thmjpr/nano_stepper/firmware/stepper_nano_zero/stepper_controller.h

/**********************************************************************
 *      Author: tstern
 *
 *	Misfit Tech invests time and resources providing this open source code,
 *	please support Misfit Tech and open-source hardware by purchasing
 *	products from Misfit Tech, www.misifittech.net!
 *
 *	Written by Trampas Stern  for Misfit Tech.
 *	BSD license, check license.txt for more information
 *	All text above, must be included in any redistribution
 *********************************************************************/
#ifndef __STEPPER_CONTROLLER_H__
#define __STEPPER_CONTROLLER_H__

#include "syslog.h"
#include "board.h"
#include "calibration.h"
#include "nonvolatile.h"

#ifdef AS5047D_ENCODER
	#include "as5047d.h"
#elif defined A1333_DRIVER
	#include "a1333.h"
#else
	#error 
#endif

#ifdef A5995_DRIVER
	#include "A5995.h"
#elif defined  STEPPER_10A
	#include "fet_driver.h"			//for the NEMA23 10A
#elif defined A4954_DRIVER
	#include "A4954.h"
#else
	#error "driver not defined"
#endif

#define N_DATA (1024)

enum class stepCtrlError {
	No_ERROR =		0,
	No_POWER =		1, //no power to motor
	No_CAL =		2, //calibration not set
	No_ENCODER =	3, //encoder not working
};

//
typedef struct {
		int32_t Kp;
		int32_t Ki;
		int32_t Kd;
} PID_t;

//
 typedef __attribute__((aligned(4))) struct {
	  int32_t microSecs;
	  int32_t desiredLoc;
	  int32_t actualLoc;
	  int32_t angle;
	  int32_t ma;
} Location_t;

//
typedef struct {
	  int32_t angle;
	  int32_t ma;
}Control_t;

#define MAX_NUM_LOCATIONS (64) //maximum number of locations to buffer

//this scales the PID parameters from Flash to floating point to fixed point int32_t values
#define CTRL_PID_SCALING (1024)

class LCD;		//Forward declaration

class StepperCtrl 
{
	private:
		volatile bool enableFeedback; //true if we are using PID control algorithm
		AS5047D encoder;
#ifdef NEMA_23_10A_HW
		FetDriver stepperDriver;
#elif defined A5995_DRIVER
		A5995 stepperDriver;
#elif defined A4954_DRIVER
		A4954 stepperDriver;
#endif

		uint16_t startUpEncoder;
		volatile int32_t ticks = 0;
		volatile Location_t locs[MAX_NUM_LOCATIONS];
		volatile int32_t locReadIndx = 0;
		volatile int32_t locWriteIndx = 0;

		volatile MotorParams_t motorParams;
		volatile SystemParams_t systemParams;
		volatile bool enabled;

		volatile int32_t loopTimeus; //time to run loop in microseconds

		volatile PID_t sPID; //simple control loop PID parameters
		volatile PID_t pPID; //positional current based PID control parameters
		volatile PID_t vPID; //velocity PID control parameters

		volatile int64_t numSteps; //this is the number of steps we have taken from our start angle

		volatile int32_t loopError;

		volatile int64_t currentLocation; //estimate of the current location from encoder feedback
		// the current location lower 16 bits is angle (0-360 degrees in 65536 steps) while upper
		// bits is the number of full rotations.

		//this is used for the velocity PID feedback
		// units are in Angles/sec where 1 Angle=360deg/65536
		volatile int64_t velocity;

		int64_t zeroAngleOffset = 0;

		//does linear interpolation of the encoder calibration table
		int32_t getAngleCalibration(int32_t encoderAngle);

		//updates the currentMeasuredAngle with our best guess where we are
		Angle sampleAngle(void);
		Angle sampleMeanEncoder(int32_t numSamples);

		float measureStepSize(void); //steps motor and estimates step size
		uint32_t measureMaxCalibrationError(void);
		void setLocationFromEncoder(void);

		void  motorReset(void);
		void updateStep(int dir, uint16_t steps);

		bool pidFeedback(int64_t desiredLoc, int64_t currentLoc, Control_t *ptrCtrl);
		bool simpleFeedback(int64_t desiredLoc, int64_t currentLoc,Control_t *ptrCtrl);
		bool vpidFeedback(int64_t desiredLoc, int64_t currentLoc,Control_t *ptrCtrl);
		int64_t getCurrentLocation(void);
		int64_t getDesiredLocation(void);
		void updateLocTable(int64_t desiredLoc, int64_t currentLoc, Control_t *ptrCtrl);
		int64_t calculatePhasePrediction(int64_t currentLoc);
		bool determineError(int64_t currentLoc, int64_t error);

	public:
		uint16_t getStartupEncoder(void) {return startUpEncoder;}
		int32_t getLocation(Location_t *ptrLoc);
		Angle getEncoderAngle(void);
		void setAngle(int64_t loc);
		int64_t getZeroAngleOffset(void);
		void PrintData(void);
		void setVelocity(int64_t vel); //set velocity for vPID mode
		int64_t getVelocity(void);
		int32_t getLoopError(void) {return loopError;}; //assume atomic read

		bool calibrationValid(void) { return calTable.calValid();}  //returns true if calbiration is good

		void updateParamsFromNVM(void);  //updates the parameters from NVM
		CalibrationTable calTable;
		//void printData(void);

		bool calibrateEncoder(LCD * lcd_d = nullptr);	//do manual calibration of the encoder
		Angle maxCalibrationError(void);				//measures the maximum calibration error as an angle

		void moveToAbsAngle(int32_t a);
		void moveToAngle(int32_t a, uint32_t ma);

		stepCtrlError begin(LCD * lcd_d = nullptr); 	//returns false if we can not use motor

		feedbackCtrl getControlMode(void) { return systemParams.controllerMode;};

		void updateSteps(int64_t steps);
		void requestStep(int dir, uint16_t steps); //requests a step, if feedback controller is off motor does not move

		bool processFeedback(void);					// does the feedback loop
		void feedback(bool enable);
		bool getFeedback(void) {return enableFeedback;}

		void encoderDiagnostics(char *ptrStr);
		int32_t measureError(void);

		//these two functions are compenstated by the zero offset
		int64_t getCurrentAngle(void);
		int64_t getDesiredAngle(void);

		void move(int dir, uint16_t steps); //forces motor to move even if feedback controller is turned off.
		void enable(bool enable);
		bool getEnable(void) {return enabled;}

		int32_t getLoopTime(void) { return loopTimeus;}

		void PID_Autotune(void);
		void setZero(void);
};

#endif //__STEPPER_CONTROLLER_H__
