thmjpr/nano_stepper/firmware/stepper_nano_zero/nzs.cpp

/*
 * nzs.cpp
 *
 *  Created on: Dec 8, 2016
 *      Author: trampas
 *
 *	
 invests time and resources providing this open source code,
 *	please support Misfit Tech and open-source hardware by purchasing
 *	products from Misfit Tech, www.misifittech.net!
 *
 *	Written by Trampas Stern  for Misfit Tech.
 *	BSD license, check license.txt for more information
 *	All text above, must be included in any redistribution
 *********************************************************************/

#include "nzs.h"
#include "commands.h"
#include "nonvolatile.h"
#include "angle.h"
#include "eeprom.h"
#include "steppin.h"
//#include "wiring_private.h"
//#include "adc_analog.h"

#pragma GCC push_options
#pragma GCC optimize ("-Ofast")

#define skip_when_no_display() if(!Lcd.displayEn()){return 0;}

//TODO:
//can show direction/step/error/enable pin status on LCD, maybe just enable?

//can show motor current or power level on LCD

//go back to bidir if marlin supports?

//adapter board required (JST see mks)

//anti-hunt and enter standby after x seconds (?), maybe not needed

/*A4950 vref in:
- 0 to 5V
- 10V/V roughly, 1.0V = 1A
- Itripmax = Vref/(10*0.1) = 3.3A max (max of dac?)

*/

eepromData_t PowerupEEPROM = { 0 };
volatile bool enableState = true;
int32_t dataEnabled = 0;	//print out
StepperCtrl stepperCtrl;	//
LCD Lcd;					//
ADC_Peripheral adc;			//

int menuInfo(int argc, char *argv[])
{
	skip_when_no_display();
	
	Lcd.showInfo();
	
	delay(900);			//show for a bit
	return 0;
}
	
int menuCalibrate(int argc, char *argv[])
{
	skip_when_no_display();
	stepperCtrl.calibrateEncoder(&Lcd);
}

int menuTestCal(int argc, char *argv[])
{
	skip_when_no_display();
	
	Angle error;
	int32_t x, y;
	char str[25];
	error = stepperCtrl.maxCalibrationError();

	x = (36000 * (int32_t)error) / ANGLE_STEPS;
	LOG("Error %d %d", (int32_t)error, x);
	y = x / 100;
	x = x - (y * 100);
	x = abs(x);
	sprintf(str, "%d.%02d deg", y, (int)x);

	Lcd.lcdShow("Cal Error", str, "");

	LOG("Calibration error %s", str);
	
#ifndef MECHADUINO_HARDWARE
	while (digitalRead(PIN_SW3) == 1)
	{
		//wait for button press
	}
	while (digitalRead(PIN_SW3) == 0)
	{
		//wait for button release
	}
#endif
	return 0;
}

//Number of steps per revolution
static  options_t stepOptions[]{
		{"200"},		//1.8 deg
		{"400"},		//0.9 deg
		{""},
};

//returns the index of the stepOptions when called with no arguments.
int motorSteps(int argc, char *argv[])
{
	if (argc == 0)
	{
		int i;
		i = NVM->motorParams.fullStepsPerRotation;
		if (i == 400)
		{
			return 1;
		}
		return 0; //default to 200
	}
	if (argc > 0)
	{
		int32_t i;
		MotorParams_t params;
		memcpy((void *)&params, (void *)&NVM->motorParams, sizeof(params));
		i = atol(argv[0]);
		if (i != params.fullStepsPerRotation)
		{
			params.fullStepsPerRotation = i;
			nvmWriteMotorParms(params);
		}
	}

	return 0;
}

//Available motor currents
static  options_t currentOptions[]{
		{"0"},			//0 is not useful
		{"100"},
		{"200"},
		{"300"},
		{"400"},
		{"500"},
		{"600"},
		{"700"},
		{"800"},
		{"900"},
		{"1000"},
		{"1100"},
		{"1200"},
		{"1300"},
		{"1400"},
		{"1500"},
		{"1600"},
		{"1700"},
		{"1800"},
		{"1900"},
		{"2000"},		//Max of A4954
		{""},
};

int motorCurrent(int argc, char *argv[])
{
	LOG("called motorCurrent %d", argc);
	if (argc == 1)
	{
		int i;
		LOG("called %s", argv[0]);
		i = atol(argv[0]);
		i = i * 100;
		MotorParams_t params;
		memcpy((void *)&params, (void *)&NVM->motorParams, sizeof(params));
		if (i != params.currentMa)
		{
			params.currentMa = i;
			nvmWriteMotorParms(params);
		}
		return i / 100;
	}
	int i;
	i = NVM->motorParams.currentMa / 100;
	LOG(" motorCurrent return %d", i);
	return i;
}

int motorHoldCurrent(int argc, char *argv[])
{
	if (argc == 1)
	{
		int i;
		i = atol(argv[0]);
		i = i * 100;
		MotorParams_t params;
		memcpy((void *)&params, (void *)&NVM->motorParams, sizeof(params));
		if (i != params.currentHoldMa)
		{
			params.currentHoldMa = i;
			nvmWriteMotorParms(params);
		}
		return i / 100;
	}
	else
	{
		int i;
		i = NVM->motorParams.currentHoldMa / 100;
		return i;
	}
}

static  options_t microstepOptions[]{
		{"1"},
		{"2"},
		{"4"},
		{"8"},
		{"16"},
		{"32"},
		{"64"},
		{"128"},
		{"256"},
		{""}
};

//argc = 1 to write new value to NVM
//argc = 0 to return current setting?
int microsteps(int argc, char *argv[])
{
	if (argc == 1)
	{
		int i, steps;
		i = atol(argv[0]);
		SystemParams_t params;
		memcpy((void *)&params, (void *)&NVM->SystemParams, sizeof(params));
		steps = 0x01 << i;
		if (steps != params.microsteps)
		{
			params.microsteps = steps;
			nvmWriteSystemParms(params);
		}
		return i;
	}
	
	int i, j;
	i = NVM->SystemParams.microsteps;
	for (j = 0; j < 9; j++)
	{
		if ((0x01 << j) == i)
		{
			return j;
		}
	}
	return 0;
}

static  options_t controlLoopOptions[]{
		{"Off"},
		{"Open"},
		{"Simple"},
		{"Pos PID"},
		{"Vel PID"},
		{""}
};

int controlLoop(int argc, char *argv[])
{
	if (argc == 1)
	{
		feedbackCtrl i = (feedbackCtrl)atol(argv[0]);
		SystemParams_t params;
		memcpy((void *)&params, (void *)&NVM->SystemParams, sizeof(params));
		if (i != params.controllerMode)
		{
			params.controllerMode = i;
			nvmWriteSystemParms(params);
		}
		return (int)i;
	}
	return (int)NVM->SystemParams.controllerMode;
}

#ifdef PIN_ERROR
static  options_t errorPinOptions[]{
		{"Error"},
		{"!Error"},
		{""}
};

int errorPin(int argc, char *argv[])
{
	if (argc == 1)
	{
		ErrorPinMode i = (ErrorPinMode)atol(argv[0]);
		SystemParams_t params;
		memcpy((void *)&params, (void *)&NVM->SystemParams, sizeof(params));
		if (i != params.errorPinMode)
		{
			params.errorPinMode = i;
			nvmWriteSystemParms(params);
		}
		return (int)i;
	}
	return (int)NVM->SystemParams.errorPinMode;
}
#endif

#ifdef PIN_ENABLE
static  options_t enablePinOptions[]{
		{"Enable"},			//Active high
		{"!Enable"},		//Active low
		{"Ignore"},			//Always enabled
		{""}
};

int enablePin(int argc, char *argv[])
{
	if (argc == 1)
	{
		EnablePinMode i = (EnablePinMode) atol(argv[0]);
		SystemParams_t params;
		memcpy((void *)&params, (void *)&NVM->SystemParams, sizeof(params));
		if (i != params.enablePinMode)
		{
			params.enablePinMode = i;
			nvmWriteSystemParms(params);
		}
		return (int)i;
	}
	return (int)NVM->SystemParams.enablePinMode;
}
#endif

static  options_t dirPinOptions[]{
		{"High CW"},
		{"High CCW"},
		{""}
};

int dirPin(int argc, char *argv[])
{
	if (argc == 1)
	{
		int i;
		i = atol(argv[0]);
		SystemParams_t params;
		memcpy((void *)&params, (void *)&NVM->SystemParams, sizeof(params));
		if ((RotationDir)i != params.dirPinRotation)
		{
			params.dirPinRotation = (RotationDir)i;
			nvmWriteSystemParms(params);
		}
		return (int)i;
	}
	return (int)NVM->SystemParams.dirPinRotation;
}

static  menuItem_t MenuMain[]{
		{"Info", menuInfo, NULL},
		{"Calibrate", menuCalibrate, NULL},
		{"Test Cal", menuTestCal, NULL},
		//		{"Mtr steps", motorSteps,stepOptions}, NOT GOOD for user to call this
		{"Motor mA", motorCurrent, currentOptions},
		{"Hold mA", motorHoldCurrent, currentOptions},
		{"Microstep", microsteps, microstepOptions},
		{"Ctlr Mode", controlLoop, controlLoopOptions}, 	//this may not be good for user to call
#ifdef PIN_ENABLE
		{"EnablePin", enablePin, enablePinOptions},
#endif
#ifdef PIN_ERROR
		{"Error Pin", errorPin, errorPinOptions},			//Need to test
#endif
		{"Dir Pin", dirPin, dirPinOptions},
		{ "", NULL}
};

static  menuItem_t MenuCal[]{
		{"Calibrate", menuCalibrate, NULL},
		//{"Test Cal", menuTestCal, NULL},
		{ "", NULL}
};


//this function is called when error pin changes as enable signal
//**FF
static void enableInput(void)
{
	static bool lastState = true;
	bool enablePin;
#ifdef PIN_ENABLE

	enablePin = digitalRead(PIN_ENABLE);	//read our enable pin

	if (enablePin != lastState)
		{
			WARNING("Enable now %d", enablePin);
			lastState = enablePin;
		}

	if (NVM->SystemParams.enablePinMode == EnablePinMode::ACTIVE_HIGH)
	{
		enableState = enablePin;
	}
	else if (NVM->SystemParams.enablePinMode == EnablePinMode::ACTIVE_LOW)
	{
		enableState = !enablePin;
	}
	else if (NVM->SystemParams.enablePinMode == EnablePinMode::ALWAYS_ON)
	{
		enableState = true;
	}
	else{}
	
#endif

#ifdef USE_STEP_DIR_SERIAL

	static uint8_t pinCFG[2];
	static uint8_t pinMux[2];
	if (enableState == false && laststate == true)
	{
		// turn the step/dir to serial port
		//save pin config for restoring
		pinCFG[0] = getPinCfg(PIN_STEP_INPUT);
		pinCFG[1] = getPinCfg(PIN_DIR_INPUT);
		pinMux[0] = getPinMux(PIN_STEP_INPUT);
		pinMux[1] = getPinMux(PIN_DIR_INPUT);

		//lets see if the step pin has interrupt enabled
		if (pinMux[0] == PORT_PMUX_PMUXE_A_Val)
		{
			EExt_Interrupts in = g_APinDescription[PIN_STEP_INPUT].ulExtInt;
			EIC->INTENCLR.reg = EIC_INTENCLR_EXTINT(1 << in); //disable the interrupt
			//we need to disable the interrupt
		}

		//now we need to set the pins to serial port peripheral (sercom0)
		setPinMux(PIN_STEP_INPUT, PORT_PMUX_PMUXE_C_Val);
		setPinMux(PIN_DIR_INPUT, PORT_PMUX_PMUXE_C_Val);

		//make sure that step pin is input with mux to peripheral
		setPinCfg(PIN_STEP_INPUT, PORT_PINCFG_PMUXEN | PORT_PINCFG_INEN | PORT_PINCFG_PULLEN);

		//make sure that dir pin is an output with mux to peripheral
		setPinCfg(PIN_DIR_INPUT, PORT_PINCFG_PMUXEN);

		Serial1.begin(STEP_DIR_BAUD);

	}
	if (enableState == true && lastState == false)
	{
		Serial1.end();
		setPinMux(PIN_STEP_INPUT, pinMux[0]);
		setPinMux(PIN_DIR_INPUT, pinMux[1]);
		setPinCfg(PIN_STEP_INPUT, pinCFG[0]);
		setPinCfg(PIN_DIR_INPUT, pinCFG[1]);
		//turn step/dir pins back to GPIO
		if (PORT_PMUX_PMUXE_A_Val == pinMux[0])
		{
			//if interrupt was enabled for step pin renable it.
			EExt_Interrupts in = g_APinDescription[PIN_STEP_INPUT].ulExtInt;
			EIC->INTENSET.reg = EIC_INTENCLR_EXTINT(1 << in); //enable the interrupt
		}

	}

#endif //USE_STEP_DIR_SERIAL
	lastState = enableState;
}

static void time_handler(void)
{
	static bool led = false;
	if (led)
		GPIO_HIGH(PIN_GREEN_LED)
	else
		GPIO_LOW(PIN_GREEN_LED)
	led = !led;
}

//Timer 5 interrupt - set to occur at rate NZS_CONTROL_LOOP_HZ.
//Handler time: 45cyc entry, 5621 complete (wha?)
//debug off: 37cyc, 4475 complete
//__attribute__((section(".data")))  not enough space to put in RAM

void TC5_Handler()
{
	int error;
	
	TC5->COUNT16.INTFLAG.bit.MC0 = 1;  	//Clear compare match flag
	interrupts(); 						//allow other interrupts
	
	error = (stepperCtrl.processFeedback());  //handle the control loop
	RED_LED(error); 					//light red LED when any error

#ifdef PIN_ERROR						//does it need to be handled here? maybe.
	
	bool level = !NVM->SystemParams.errorLogic;
	//GPIO_OUTPUT(PIN_ERROR); should be covered elsewhere?
	
	if(error)
	{
		if (level)
			GPIO_HIGH(PIN_ERROR)
		else
			GPIO_LOW(PIN_ERROR)
	}
	else
	{
		if (!level)
			GPIO_HIGH(PIN_ERROR)	
		else
			GPIO_LOW(PIN_ERROR)
	}
#else
	if (NVM->SystemParams.errorPinMode == ERROR_PIN_MODE_ERROR)
	{
		GPIO_OUTPUT(PIN_ERROR);
		if (error)
		{
				//assume high is inactive and low is active on error pin
			digitalWrite(PIN_ERROR, LOW);
		}
		else
		{
			digitalWrite(PIN_ERROR, HIGH);
		}
	}
#endif

}

//check the NVM and set to defaults if there is any
void validateAndInitNVMParams(void)
{
	if (false == NVM->sPID.parametersValid)
	{
		LOG("sPID invalid %0x %0x %0x, %0x addr %0x", NVM->sPID.Ki, NVM->sPID.Kp, NVM->sPID.Kd, NVM->sPID.parametersValid, &NVM->sPID.parametersValid);
		nvmWrite_sPID(0.9, 0.0001, 0.01);
	}

	if (false == NVM->pPID.parametersValid)
	{
		LOG("pPID invalid %0x", NVM->pPID.parametersValid);
		nvmWrite_pPID(1.0, 0.001, 0.01);
	}

	if (false == NVM->vPID.parametersValid)
	{
		nvmWrite_vPID(2.0, 1.0, 1.0);
	}

	if (false == NVM->SystemParams.parametersValid)
	{
		LOG("sys param invalid");
		SystemParams_t params;
		params.microsteps = 16;
		params.controllerMode = feedbackCtrl::SIMPLE;
		params.dirPinRotation = RotationDir::CW; 				//default to clockwise rotation when dir is high
		params.errorLimit = (int32_t)ANGLE_FROM_DEGREES(1.8);
		params.errorPinMode = ErrorPinMode::ACTIVE_LOW; 		//default to active low
		params.enablePinMode = EnablePinMode::ALWAYS_ON;		//default to always on
		params.homePin = -1;
		params.errorLogic = false;
		params.enableLogic = false;
		params.homeAngleDelay = ANGLE_FROM_DEGREES(10);
		nvmWriteSystemParms(params);
	}
	//the motor parameters are check in the stepper_controller code
	// as that there we can auto set much of them.
}

void SYSCTRL_Handler(void)
{
	if (SYSCTRL->INTFLAG.reg & SYSCTRL_INTFLAG_BOD33DET)
	{
		eepromFlush(); //flush the eeprom
		SYSCTRL->INTFLAG.reg |= SYSCTRL_INTFLAG_BOD33DET;
	}
}

// Wait for synchronization of registers between the clock domains
static __inline__ void syncBOD33(void) __attribute__((always_inline, unused));
static void syncBOD33(void) 
{
	while (SYSCTRL->PCLKSR.bit.BOD33RDY == 1)
	{
	}
}

//Configure brownout level
static void configure_bod(void)
{
	SYSCTRL->BOD33.reg = SYSCTRL_BOD33_ACTION_INTERRUPT |  //generate interrupt when BOD is triggered
	SYSCTRL_BOD33_LEVEL(40) |	//about 3V, was 48 (3.2V)
	SYSCTRL_BOD33_HYST |		//enable hysteresis
	SYSCTRL_BOD33_ENABLE;		//turn module on

	LOG("BOD33 %02X", SYSCTRL->BOD33.reg);
	SYSCTRL->INTENSET.reg |= SYSCTRL_INTENSET_BOD33DET;

	NVIC_SetPriority(SYSCTRL_IRQn, 1);			//make highest priority as we need to save eeprom //save what?
	
	NVIC_EnableIRQ(SYSCTRL_IRQn);				// Enable InterruptVector
}

//
void NZS::begin(void)
{
	int to = 20;
	volatile stepCtrlError stepCtrlError;

	boardSetupPins();		//set up the pins correctly on the board.
	RED_LED(true);			//
	adc.begin();			//enable ADC

	Serial5.begin(SERIAL_BAUD);	//setup the serial port for syslog

#ifndef CMD_SERIAL_PORT
	SysLogInit(&Serial5, LOG_DEBUG); //use SWO for the sysloging
	//pinPeripheral(PIN_TXD, PIO_SERCOM_ALT);
	//pinPeripheral(PIN_RXD, PIO_SERCOM_ALT);
#else
	SysLogInit(NULL, LOG_WARNING);
#endif
	
	LOG("Power up!");

	if (digitalRead(PIN_USB_PWR))
	{
		//start up the USB serial interface
		SerialUSB.begin(SERIAL_BAUD);
		
		//wait for USB serial port to come alive
		while (!SerialUSB)
		{
			to--;
			if (to == 0)
			{
				break;
			}
			delay(500);
		};     //wait for serial
	}
	else
	{
		WARNING("USB Not connected");
	}

	validateAndInitNVMParams();

	LOG("EEPROM INIT");

	if (EEPROM_OK == eepromInit()) //init the EEPROM
	{
		eepromRead((uint8_t *)&PowerupEEPROM, sizeof(PowerupEEPROM));
	}

	configure_bod(); 					//configure the brownout detect

	LOG("Testing LCD");
	Lcd.begin(&stepperCtrl, &adc);		//Attempt connection to LCD
	Lcd.showSplash();					//Splash screen

	LOG("command init!");
	commandsInit();					//setup command handler system
	stepCtrlError = stepCtrlError::No_CAL;
		
	
	while (stepCtrlError::No_ERROR != stepCtrlError)
	{
		LOG("init the stepper controller");
		stepCtrlError = stepperCtrl.begin(&Lcd); //start controller before accepting step inputs

		//todo we need to handle error on LCD and through command line
		if(stepCtrlError::No_POWER == stepCtrlError)
		{
			SerialUSB.println("Appears that there is no Motor Power");			//No motor power, driver IC dead, or bad cable to motor
			SerialUSB.println("Connect motor power!");
			Lcd.lcdShow("Waiting:", "Motor", "Power");

			while (stepCtrlError::No_POWER == stepCtrlError)
			{
				stepCtrlError = stepperCtrl.begin(&Lcd);  //start controller before accepting step inputs
			}
		}
		
		//TODO: allow setting motor current prior to calibration...
		if (stepCtrlError:: No_CAL == stepCtrlError)
		{
			SerialUSB.println("You need to Calibrate");
			Lcd.lcdShow("   NOT ", "Calibrated", " ");
			delay(800);
			Lcd.setMenu(MenuCal);
			Lcd.forceMenuActive();

			//TODO add code here for LCD and command line loop
			while(false == stepperCtrl.calibrationValid())
			{
				commandsProcess(); //handle commands
				Lcd.process();
			}
			Lcd.setMenu(NULL);
		}

		if (stepCtrlError::No_ENCODER == stepCtrlError)
		{
			SerialUSB.println("AS5047D not working");
			SerialUSB.println(" try disconnecting power from board for 15+mins");
			SerialUSB.println(" you might have to short out power pins to ground");
			Lcd.lcdShow("Encoder", " Error!", " REBOOT");

			while (1)
			{

			}
		}

	}

	stepPinSetup();			//setup the step pin		//race issue where TC5 is triggering before TC2 setup.
	Lcd.setMenu(MenuMain);
	
#ifdef PIN_ENABLE
	//attachInterrupt(digitalPinToInterrupt(PIN_ENABLE), enableInput, CHANGE);
	NVIC_SetPriority(EIC_IRQn, 0); //set port A interrupt as highest priority		//**FF
#else
	//attachInterrupt(digitalPinToInterrupt(PIN_ERROR), enableInput, CHANGE);
#endif

	SmartPlanner.begin(&stepperCtrl);
	RED_LED(false);
	LOG("SETUP DONE!");
}

//
void printLocation(void)
{
	char buf[128] = { 0 };
	Location_t loc;
	int32_t n, i, len;
	int32_t pktSize;

	if (dataEnabled == 0)
	{
		//RED_LED(false);
		return;
	}

	//the packet length for binary print is 12bytes
	// assuming rate of 6Khz this would be 72,000 baud
	i = 0;
	n = stepperCtrl.getLocation(&loc);
	if (n == -1)
	{
		//RED_LED(false);
		return;
	}

	len = 0;
	pktSize = sizeof(Location_t) + 1; //packet lenght is size location plus sync byte

	//binary write
	while ((n >= 0) && (len <= (128 - pktSize)))
	{
		memcpy(&buf[len], &loc, sizeof(Location_t));
		len += sizeof(Location_t);
		buf[len] = 0xAA; //sync
		len++;
		buf[len] = sizeof(Location_t); //data len
		len++;
		n = stepperCtrl.getLocation(&loc);
		i++;
	}
	SerialUSB.write(buf, len);

	//hex write
	// hex write is 29 bytes per tick, @ 6khz this 174000 baud
	//   while(n>=0 && (i*29)<(200-29))
	//   {
	//      sprintf(buf,"%s%08X\t%08X\t%08X\n\r",buf,loc.microSecs,loc.desiredLoc,loc.actualLoc);
	//      n=stepperCtrl.getLocation(&loc);
	//      i++;
	//   }
	//   SerialUSB.write(buf,strlen(buf));

	if (n <= 0)
	{
		RED_LED(false);
	}
	else
	{
		RED_LED(true);
	}
	return;
}

//
void NZS::loop(void)
{
	eepromData_t eepromData;

	   if (dataEnabled == 1)
	   {
	      LOG("loop time is %dus",stepperCtrl.getLoopTime());
	   }

	// Read the enable pin and update
	// this is also done as an edge interrupt but does not always see to trigger the ISR.
	enableInput(); //**FF interrupt should always occur, check..

	if (enableState != stepperCtrl.getEnable())
	{
		stepperCtrl.enable(enableState);
	}
	
	//Continuously update EEPROM with current position 
	if(UPDATE_EEPROM)
	{
	eepromData.angle = stepperCtrl.getCurrentAngle();
	eepromData.encoderAngle = stepperCtrl.getEncoderAngle();
	eepromData.valid = 1;
	eepromWriteCache((uint8_t *)&eepromData, sizeof(eepromData));
	}
	
	commandsProcess();		//handle commands
	Lcd.process();			//update display and process keypresses - approx 1000 cycles
	//stepperCtrl.PrintData(); //prints steps and angle to serial USB.
	printLocation();		//print out the current location
	
	//if millis() 500 -> measure temperature, etc. stuff thats not required often
	

	return;
}

#pragma GCC pop_options
