thmjpr/nano_stepper/firmware/stepper_nano_zero/A4954.h

/**********************************************************************
 *      Author: tstern
 *
 *	Misfit Tech invests time and resources providing this open source code,
 *	please support Misfit Tech and open-source hardware by purchasing
 *	products from Misfit Tech, www.misifittech.net!
 *
 *	Written by Trampas Stern  for Misfit Tech.
 *	BSD license, check license.txt for more information
 *	All text above, must be included in any redistribution
 *********************************************************************/
#ifndef __A4954__H__
#define __A4954__H__
#include <Arduino.h>
#include "board.h"
#include "angle.h"
#include "sine.h"

#define A4954_NUM_MICROSTEPS (256)
#define A4954_MIN_TIME_BETWEEN_STEPS_MICROS  (1000)

//prevent someone for making a mistake with the code
#if ((A4954_NUM_MICROSTEPS*4) != SINE_STEPS)
#error "SINE_STEPS must be 4x of Micro steps for the move function"
#endif

/*
 *  When it comes to the stepper driver if we use angles
 *  we will always have a rounding error. For example
 *  a 0-65536(360) angle for 1.8 degree step is 327.68 so
 *  if you increment 200 of these as 327 you have a 13.6 error
 *  after one rotation.
 *  If you use floating point the effect is the same but takes longer.
 *
 *  The only error-less accumulation system is to use native units, ie full
 *  steps and microsteps.
 *
 */

class A4954
{
private:
	uint32_t lastStepMicros = 0;    // time in microseconds that last step happened
	bool forwardRotation = true;    //
	volatile bool enabled = true;   //
	void enableTCC0(uint8_t percent);               //
	void setupDAC(void);                            //
	void setDAC(uint32_t DAC1, uint32_t DAC2);      //
	void setMotorPWM(uint8_t percent);       //

public:
	void begin(void);
	int32_t move(int32_t stepAngle, uint32_t mA);                               //moves motor where the modulo of A4954_NUM_MICROSTEPS is a full step.
	uint32_t microsSinceStep(void) { return micros() - lastStepMicros; };       //
	void setRotationDirection(bool forward) { forwardRotation = forward; };     //
	void enable(bool enable);                                                   //Setup pins to A4954
	void limitCurrent(uint8_t percent);                                         //Higher more current
};

enum class drvStates
{
	Forward = 0, 	    //
	Reverse = 1, 	   //
	Brake = 2, 	      //
	HiZ = 3         //Coast
};

#endif //__A4954__H__
